retrobuiltRyan/4in_Tinitron_Monitor/wedge.3MF

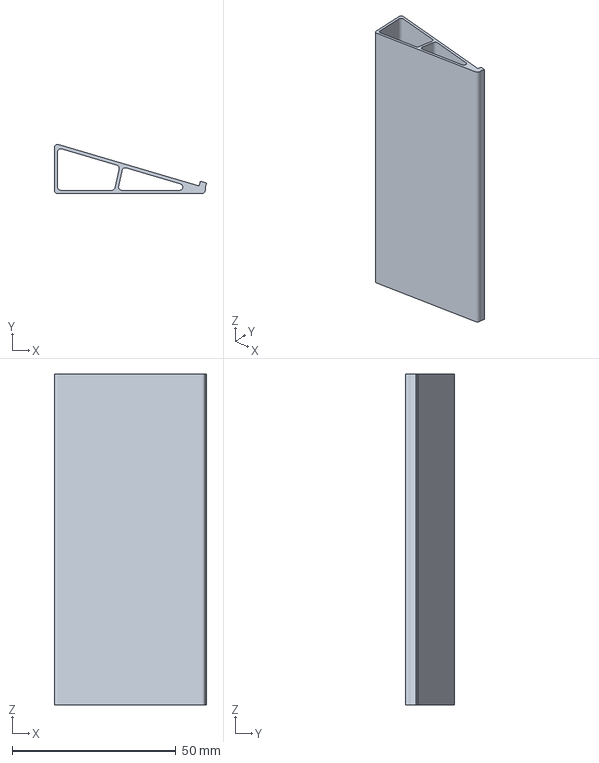
[picture p15: CAD file, 2024-04-13]
wedge.3MF
46.5 x 15.0 x 101.0 mm
